FPGA-Computer/TUSB-Blaster/USB client source code/hardware.c

/*-----------------------------------------------------------------------------
 * Hardware-dependent code for usb_jtag
 *-----------------------------------------------------------------------------
 * Copyright (C) 2007 Kolja Waschk, ixo.de
 *-----------------------------------------------------------------------------
 * This code is part of usbjtag. usbjtag is free software; you can redistribute
 * it and/or modify it under the terms of the GNU General Public License as
 * published by the Free Software Foundation; either version 2 of the License,
 * or (at your option) any later version. usbjtag is distributed in the hope
 * that it will be useful, but WITHOUT ANY WARRANTY; without even the implied
 * warranty of MERCHANTABILITY or FITNESS FOR A PARTICULAR PURPOSE.  See the
 * GNU General Public License for more details.  You should have received a
 * copy of the GNU General Public License along with this program in the file
 * COPYING; if not, write to the Free Software Foundation, Inc., 51 Franklin
 * St, Fifth Floor, Boston, MA  02110-1301  USA
 *-----------------------------------------------------------------------------
 */

#include "main.h"

void ProgIO_Poll(void)    {}
// These aren't called anywhere in usbjtag.c, but I plan to do so...
void ProgIO_Enable(void)  {}
void ProgIO_Disable(void) {}
void ProgIO_Deinit(void)  {}

void ProgIO_Init(void)
{
  /* The following code depends on your actual circuit design.
     Make required changes _before_ you try the code! */
  TDO = 1;		// Input 
  }

void ProgIO_Set_State(unsigned char d)
{ 
  TCK = (d & bm_TCK)?1:0;
  TDI = (d & bm_TDI)?1:0;
  TMS = (d & bm_TMS)?1:0;
  
  MCR = ((d & (bm_TRST|bm_SRST))<<2)^(bm_TRST|bm_SRST);
 }

unsigned char ProgIO_Set_Get_State(unsigned char d)
{ 
    ProgIO_Set_State(d);
    return (TDO);
 }

void  Multibyte_ProgIO(word m, xubyte *pointer1)
{ pointer1;
				
__asm
	mov	r2,_Multibyte_ProgIO_PARM_2
	mov	r3,(_Multibyte_ProgIO_PARM_2 + 1)
__endasm;

       while(m--) 	
__asm
	mov	dpl,r2			//    ProgIO_ShiftOut(*(pointer1++));
	mov	dph,r3
	movx	a,@dptr
	mov	r3,a
	inc	dptr
	mov	r2,dpl
	mov	r3,dph	
	mov	a,r3		
	lcall	__ProgIO_ShiftOut_
  __endasm;  	
  }
 
//-----------------------------------------------------------------------------

   /* Shift out byte C: 
   *
   * 8x {
   *   Output least significant bit on TDI
   *   Raise TCK
   *   Shift c right
   *   Lower TCK
   * }
   */
	
void ProgIO_ShiftOut(unsigned char c)
{

  (void)c; /* argument passed in DPL */

  __asm
        MOV  A,DPL
	
__ProgIO_ShiftOut_:
        ;; Bit0
        RRC  A
        MOV  _TDI,C
        SETB _TCK
        ;; Bit1
        RRC  A
        CLR  _TCK
        MOV  _TDI,C
        SETB _TCK
        ;; Bit2
        RRC  A
        CLR  _TCK
        MOV  _TDI,C
        SETB _TCK
        ;; Bit3
        RRC  A
        CLR  _TCK
        MOV  _TDI,C
        SETB _TCK
        ;; Bit4
        RRC  A
        CLR  _TCK
        MOV  _TDI,C
        SETB _TCK
        ;; Bit5
        RRC  A
        CLR  _TCK
        MOV  _TDI,C
        SETB _TCK
        ;; Bit6
        RRC  A
        CLR  _TCK
        MOV  _TDI,C
        SETB _TCK
        ;; Bit7
        RRC  A
        CLR  _TCK
        MOV  _TDI,C
        SETB _TCK
        NOP 
        CLR  _TCK
  __endasm;
}

/*
;; For ShiftInOut, the timing is a little more
;; critical because we have to read _TDO/shift/set _TDI
;; when _TCK is low. But 20% duty cycle at 48/4/5 MHz
;; is just like 50% at 6 Mhz, and that's still acceptable
*/

unsigned char ProgIO_ShiftInOut_JTAG(unsigned char c)
{
  /* Shift out byte C, shift in from TDO:
   *
   * 8x {
   *   Read carry from TDO
   *   Output least significant bit on TDI
   *   Raise TCK
   *   Shift c right, append carry (TDO) at left
   *   Lower TCK
   * }
   * Return c.
   */

   (void)c; /* argument passed in DPL */

  __asm
        MOV  A,DPL

        ;; Bit0
        MOV  C,_TDO
        RRC  A
        MOV  _TDI,C
        SETB _TCK
        CLR  _TCK
        ;; Bit1
        MOV  C,_TDO
        RRC  A
        MOV  _TDI,C
        SETB _TCK
        CLR  _TCK
        ;; Bit2
        MOV  C,_TDO
        RRC  A
        MOV  _TDI,C
        SETB _TCK
        CLR  _TCK
        ;; Bit3
        MOV  C,_TDO
        RRC  A
        MOV  _TDI,C
        SETB _TCK
        CLR  _TCK
        ;; Bit4
        MOV  C,_TDO
        RRC  A
        MOV  _TDI,C
        SETB _TCK
        CLR  _TCK
        ;; Bit5
        MOV  C,_TDO
        RRC  A
        MOV  _TDI,C
        SETB _TCK
        CLR  _TCK
        ;; Bit6
        MOV  C,_TDO
        RRC  A
        MOV  _TDI,C
        SETB _TCK
        CLR  _TCK
        ;; Bit7
        MOV  C,_TDO
        RRC  A
        MOV  _TDI,C
        SETB _TCK
        CLR  _TCK

        MOV  DPL,A
        ret
  __endasm;

  /* return value in DPL */

  return c;
}
