FPGA-Computer/TUSB-Blaster/USB client source code/usb def.h

/*
 * usb_driver.h - A relatively easy to use C interface to the USB
 *                hardware on the TUSB3210/TUSB3410 chips. This module
 *                implements many standard commands defined in the USB
 *                spec, and allows vendor-specific commands to be
 *                defined externally.
 *
 * Copyright (C) 2004-2005 Micah Dowty
 *
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
 */
#ifndef __USB_DEF_H
#define __USB_DEF_H

/*
 * Device and/or Interface Class codes
 */
#define USB_CLASS_PER_INTERFACE				0	/* for DeviceClass */
#define USB_CLASS_AUDIO			    		1
#define USB_CLASS_COMM			    		2
#define USB_CLASS_HID			    		3
#define USB_CLASS_PHYSICAL		    		5
#define USB_CLASS_STILL_IMAGE				6
#define USB_CLASS_PRINTER		    		7
#define USB_CLASS_MASS_STORAGE				8
#define USB_CLASS_HUB			    		9
#define USB_CLASS_CDC_DATA		    		0x0a
#define USB_CLASS_CSCID			    		0x0b	/* chip+ smart card */
#define USB_CLASS_CONTENT_SEC				0x0d	/* content security */
#define USB_CLASS_APP_SPEC		    			0xfe
#define USB_CLASS_VENDOR_SPEC				0xff

/*
 * USB types
 */
#define USB_TYPE_MASK			    		(3<<5)
#define USB_TYPE_STANDARD		    		(0<<5)
#define USB_TYPE_CLASS			    		(1<<5)
#define USB_TYPE_VENDOR			    		(2<<5)
#define USB_TYPE_RESERVED		    		(3<<5)

/*
 * USB recipients
 */
#define USB_RECIP_MASK			    		0x1f
#define USB_RECIP_DEVICE		    		0x00
#define USB_RECIP_INTERFACE		    		0x01
#define USB_RECIP_ENDPOINT		    		0x02
#define USB_RECIP_OTHER			    		0x03

/*
 * USB directions
 */
#define USB_DIR_OUT			        	0		/* to device */
#define USB_DIR_IN			        	0x80    	/* to host */

/*
 * Descriptor types
 */
#define USB_DT_DEVICE			    		0x01
#define USB_DT_CONFIG			    		0x02
#define USB_DT_STRING			    		0x03
#define USB_DT_INTERFACE		    		0x04
#define USB_DT_ENDPOINT			    		0x05

#define USB_DT_DEVICE_QUALIFIER          		0x06
#define USB_DT_OTHER_SPEED_CONFIGURATION 		0x07
#define USB_DT_INTERFACE_POWER           		0x08

#define USB_DT_HID			        	(USB_TYPE_CLASS | 0x01)
#define USB_DT_REPORT			    		(USB_TYPE_CLASS | 0x02)
#define USB_DT_PHYSICAL					(USB_TYPE_CLASS | 0x03)
#define USB_DT_HUB			        	(USB_TYPE_CLASS | 0x09)

/*
 * Descriptor sizes per descriptor type
 */
#define USB_DT_DEVICE_SIZE		    	18
#define USB_DT_CONFIG_SIZE		  	9
#define USB_DT_INTERFACE_SIZE			9
#define USB_DT_ENDPOINT_SIZE			7
#define USB_DT_ENDPOINT_AUDIO_SIZE		9	/* Audio extension */
#define USB_DT_HUB_NONVAR_SIZE			7
#define USB_DT_HID_SIZE				9

/*
 * Endpoints
 */
#define USB_ENDPOINT_NUMBER_MASK	0x0f	/* in bEndpointAddress */
#define USB_ENDPOINT_DIR_MASK		0x80

#define USB_ENDPOINT_XFERTYPE_MASK	0x03	/* in bmAttributes */
#define USB_ENDPOINT_XFER_CONTROL	0
#define USB_ENDPOINT_XFER_ISOC		1
#define USB_ENDPOINT_XFER_BULK		2
#define USB_ENDPOINT_XFER_INT		3

/*
 * Standard requests
 */
#define USB_REQ_GET_STATUS		0x00
#define USB_REQ_CLEAR_FEATURE		0x01
#define USB_REQ_SET_FEATURE		0x03
#define USB_REQ_SET_ADDRESS		0x05
#define USB_REQ_GET_DESCRIPTOR		0x06
#define USB_REQ_SET_DESCRIPTOR		0x07
#define USB_REQ_GET_CONFIGURATION	0x08
#define USB_REQ_SET_CONFIGURATION	0x09
#define USB_REQ_GET_INTERFACE		0x0A
#define USB_REQ_SET_INTERFACE		0x0B
#define USB_REQ_SYNCH_FRAME		0x0C

/*
 * HID requests
 */
#define USB_REQ_GET_REPORT		0x01
#define USB_REQ_GET_IDLE		0x02
#define USB_REQ_GET_PROTOCOL		0x03
#define USB_REQ_SET_REPORT		0x09
#define USB_REQ_SET_IDLE		0x0A
#define USB_REQ_SET_PROTOCOL		0x0B

struct usb_ctrlrequest                  // Setup packet
{
  ubyte bRequestType;
  ubyte bRequest;
  uword wValue;
  uword wIndex;
  uword wLength;
 };

struct usb_descriptor_header
{
  ubyte  bLength;
  ubyte  bDescriptorType;
};

struct usb_device_descriptor
{
  ubyte  bLength;
  ubyte  bDescriptorType;
  uword  bcdUSB;
  ubyte  bDeviceClass;
  ubyte  bDeviceSubClass;
  ubyte  bDeviceProtocol;
  ubyte  bMaxPacketSize0;
  uword  idVendor;
  uword  idProduct;
  uword  bcdDevice;
  ubyte  iManufacturer;
  ubyte  iProduct;
  ubyte  iSerialNumber;
  ubyte  bNumConfigurations;
 };

struct usb_config_descriptor 
{
  ubyte  bLength;
  ubyte  bDescriptorType;
  uword  wTotalLength;
  ubyte  bNumInterfaces;
  ubyte  bConfigurationValue;
  ubyte  iConfiguration;
  ubyte  bmAttributes;
  ubyte  MaxPower;
 };

struct usb_interface_descriptor
{
  ubyte  bLength;
  ubyte  bDescriptorType;
  ubyte  bInterfaceNumber;
  ubyte  bAlternateSetting;
  ubyte  bNumEndpoints;
  ubyte  bInterfaceClass;
  ubyte  bInterfaceSubClass;
  ubyte  bInterfaceProtocol;
  ubyte  iInterface;
 };

struct usb_endpoint_descriptor
{
  ubyte  bLength;
  ubyte  bDescriptorType;
  ubyte  bEndpointAddress;
  ubyte  bmAttributes;
  uword  wMaxPacketSize;
  ubyte  bInterval;
 };

#endif /* __USB_DEF_H */
